tonykoop/djembe/analysis/helmholtz-fem/figures/mode-shapes-L.png

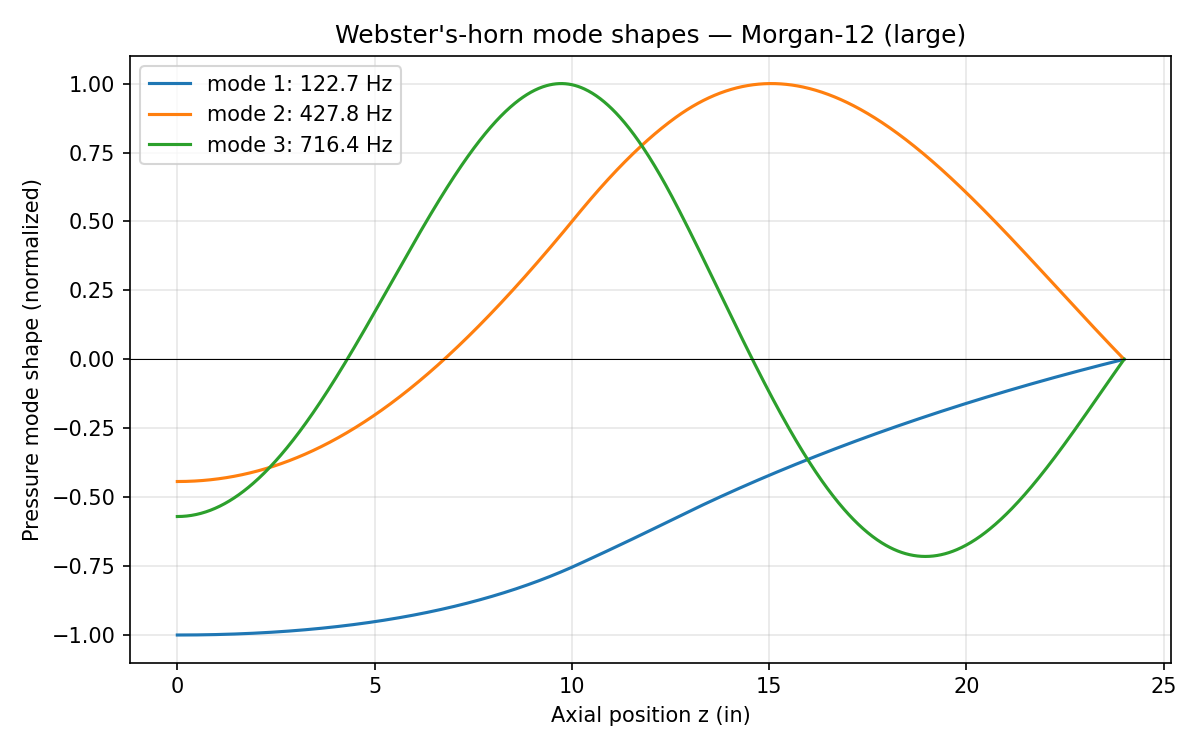
analysis/helmholtz-fem/figures/mode-shapes-L.png
