tonykoop/djembe/arena/round2/stave-djembe-arena-winner.png

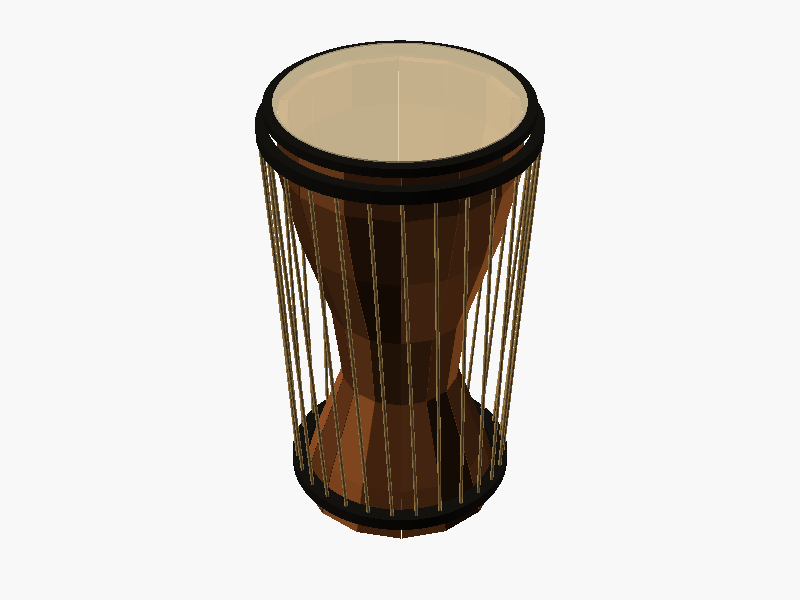
arena/round2/stave-djembe-arena-winner.png
