tonykoop/djembe/CAD/Djembe/Djimbey C.PNG

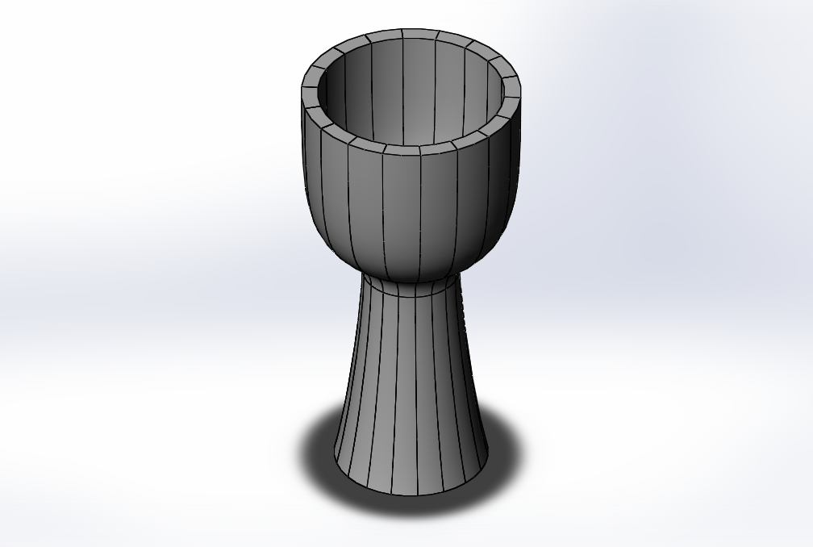
CAD/Djembe/Djimbey C.PNG
