tonykoop/djembe/CAD/Segmented Djembe/large-djembe/Large Djembe Segmented Pattern 1.PNG

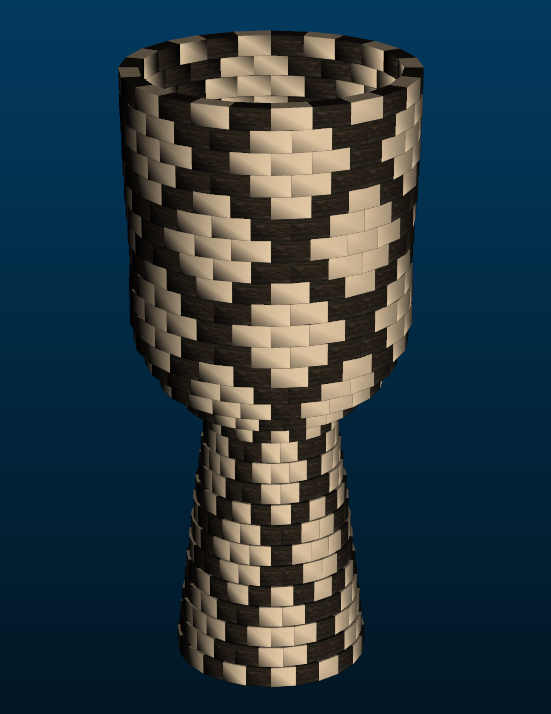
CAD/Segmented Djembe/large-djembe/Large Djembe Segmented Pattern 1.PNG
