tonykoop/djembe/CAD/Segmented Djembe/large-djembe/Large Djembe Segmented Pattern 2.PNG

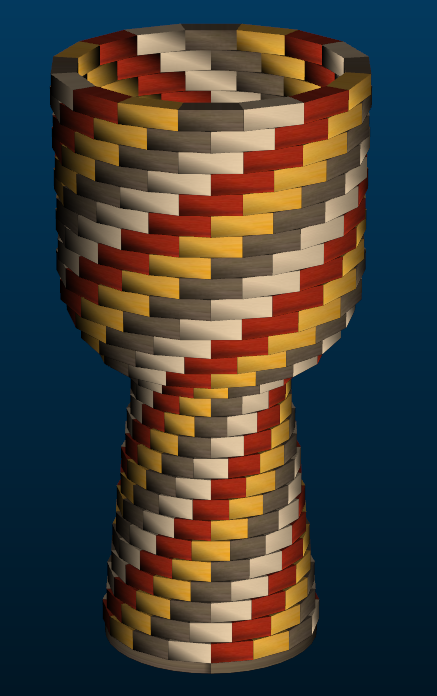
CAD/Segmented Djembe/large-djembe/Large Djembe Segmented Pattern 2.PNG
