tonykoop/djembe/CAD/Segmented Djembe/large-djembe/Large Djembe Segmented Pattern 3.PNG

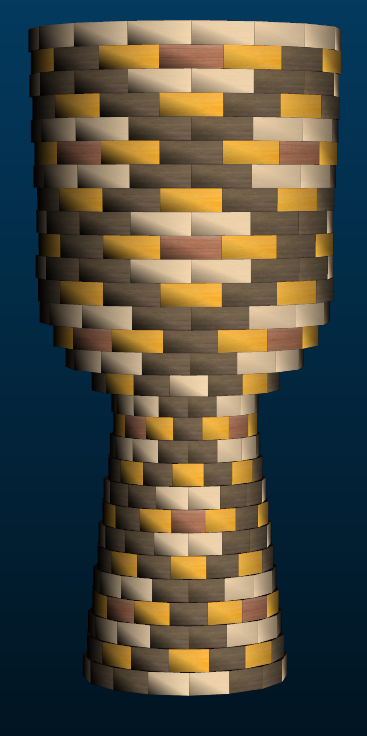
CAD/Segmented Djembe/large-djembe/Large Djembe Segmented Pattern 3.PNG
