tonykoop/djembe/CAD/Segmented Djembe/large-djembe/Large Djembe Segmented Pattern 4.PNG

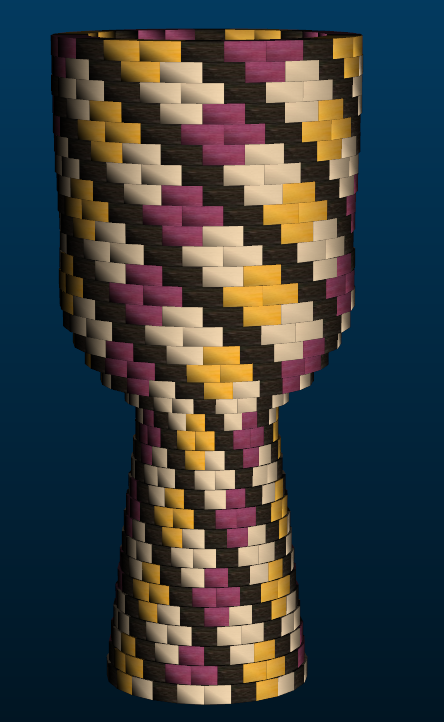
CAD/Segmented Djembe/large-djembe/Large Djembe Segmented Pattern 4.PNG
