tonykoop/djembe/CAD/Segmented Djembe/small-djembe/Small Djembe Segmented Pattern 1.PNG

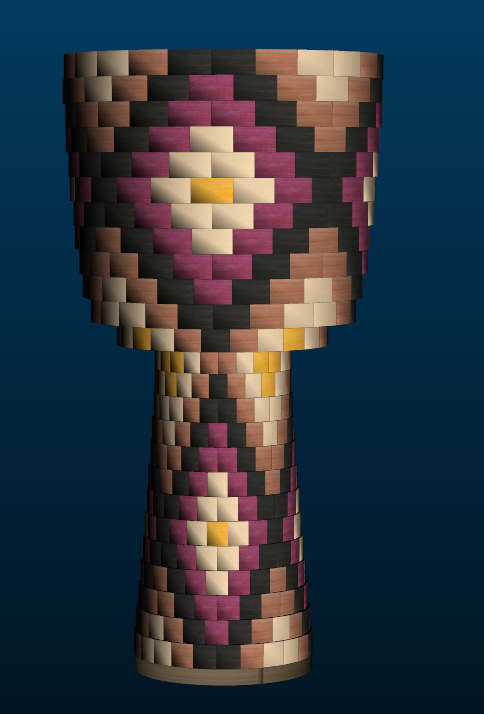
CAD/Segmented Djembe/small-djembe/Small Djembe Segmented Pattern 1.PNG
