tonykoop/djembe/CAD/Segmented Djembe/small-djembe/Small Djembe Segmented Pattern 2.PNG

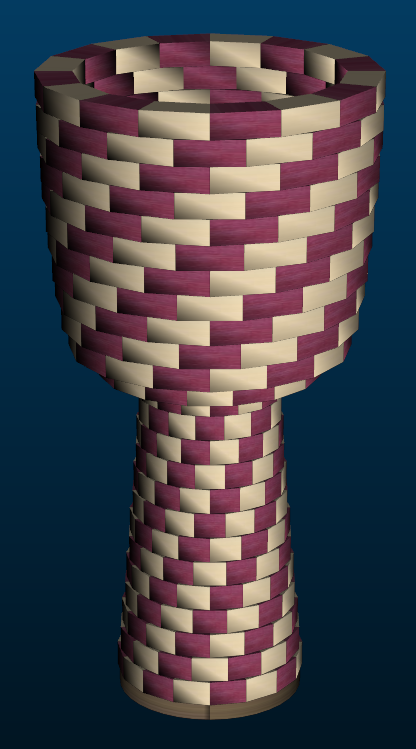
CAD/Segmented Djembe/small-djembe/Small Djembe Segmented Pattern 2.PNG
