tonykoop/djembe/CAD/Segmented Djembe/small-djembe/Small Djembe Segmented Pattern 3.PNG

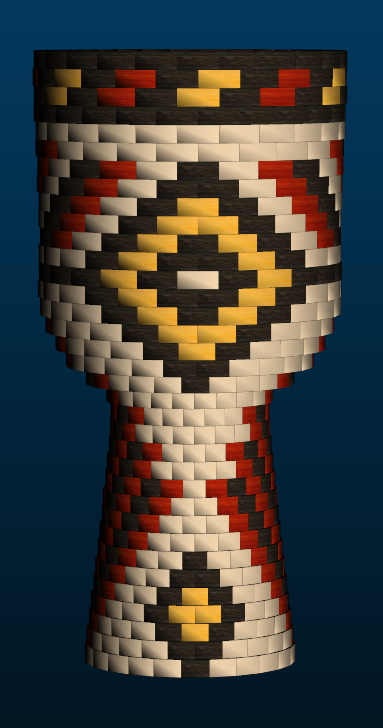
CAD/Segmented Djembe/small-djembe/Small Djembe Segmented Pattern 3.PNG
