tonykoop/djembe/drawings/img20260425_23594038.png

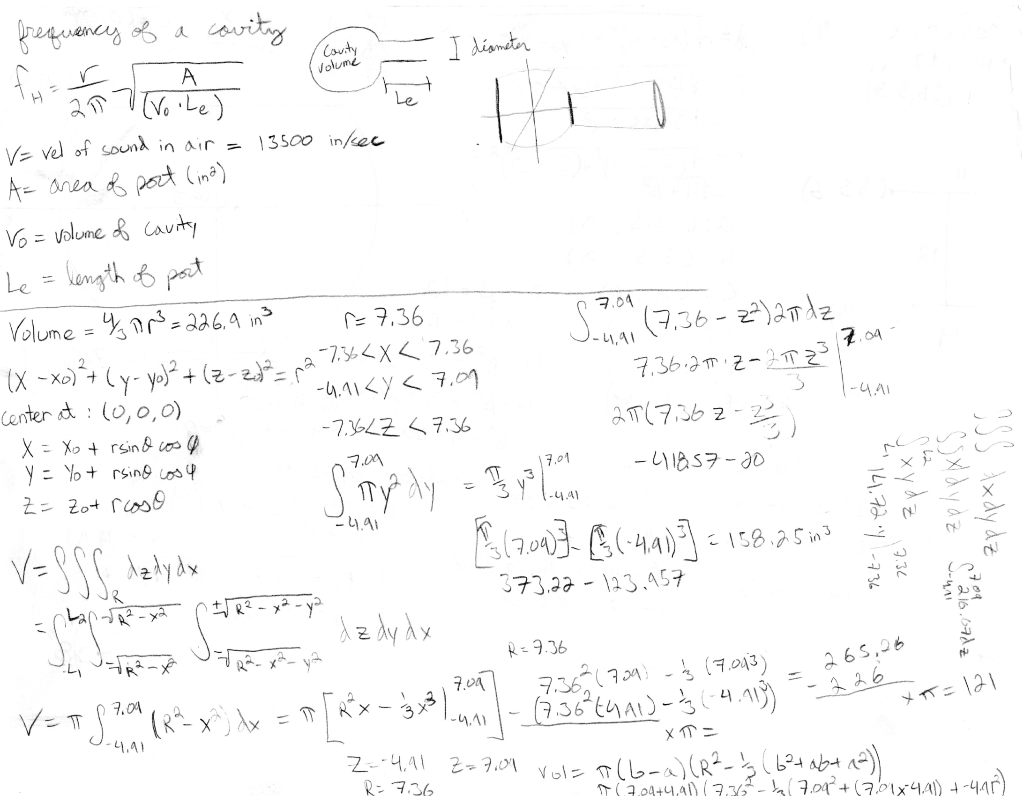
drawings/img20260425_23594038.png
