tonykoop/djembe/drawings/img20260426_00000252.png

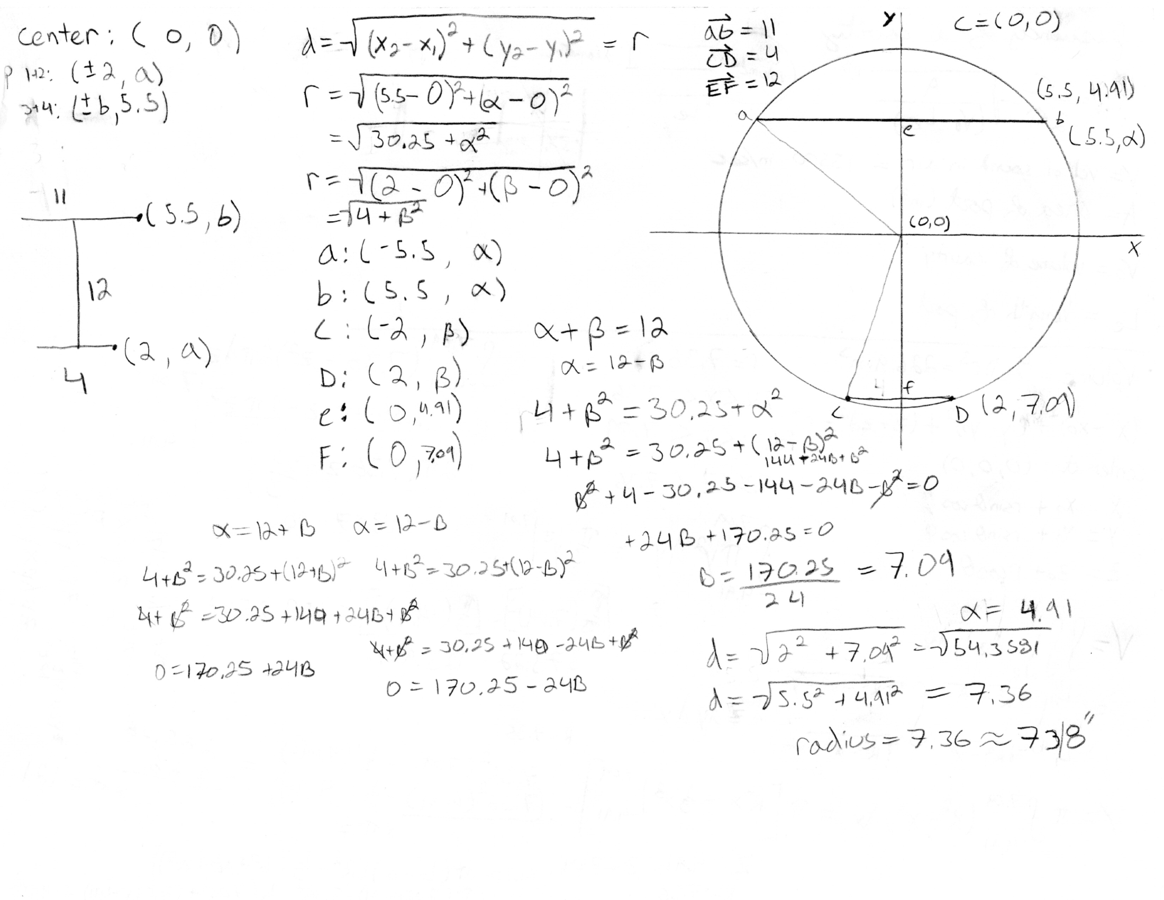
drawings/img20260426_00000252.png
