tonykoop/djembe/drawings/img20260426_00003487.png

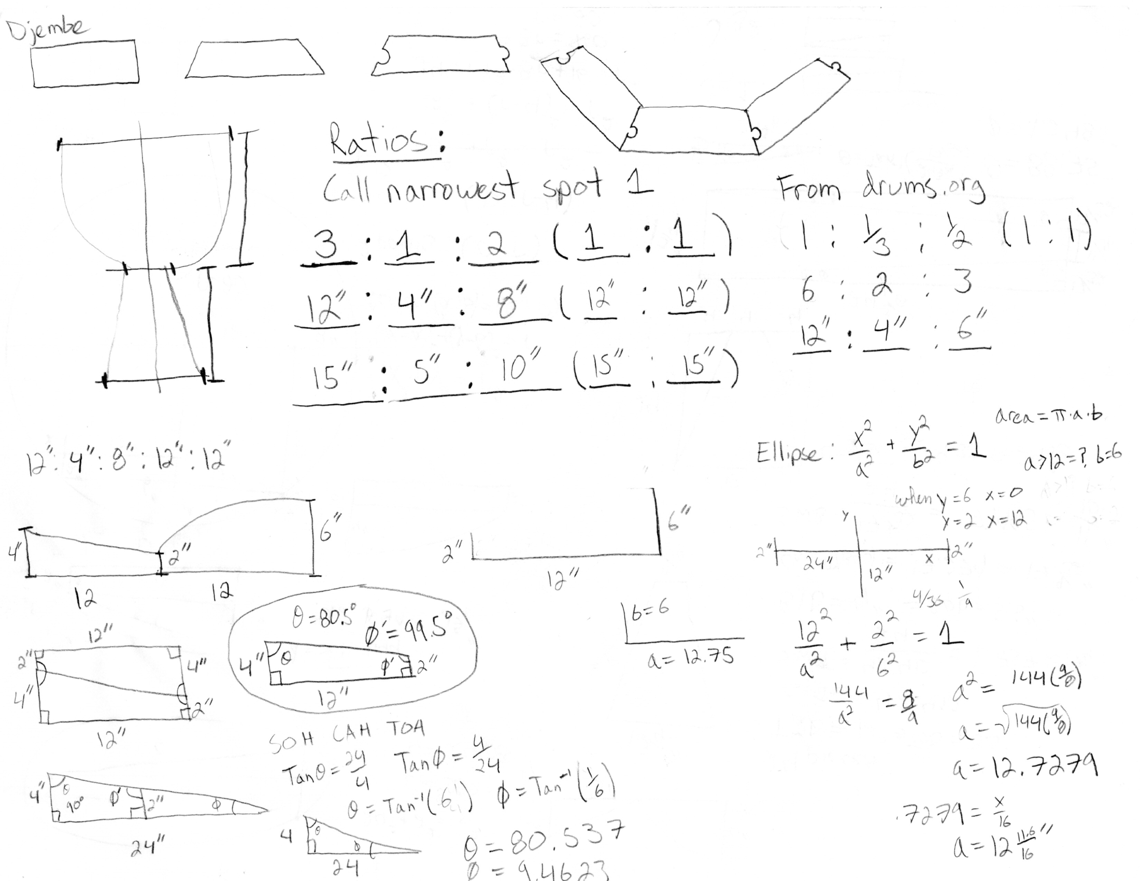
drawings/img20260426_00003487.png
