tonykoop/djembe/drawings/img20260426_00005662.png

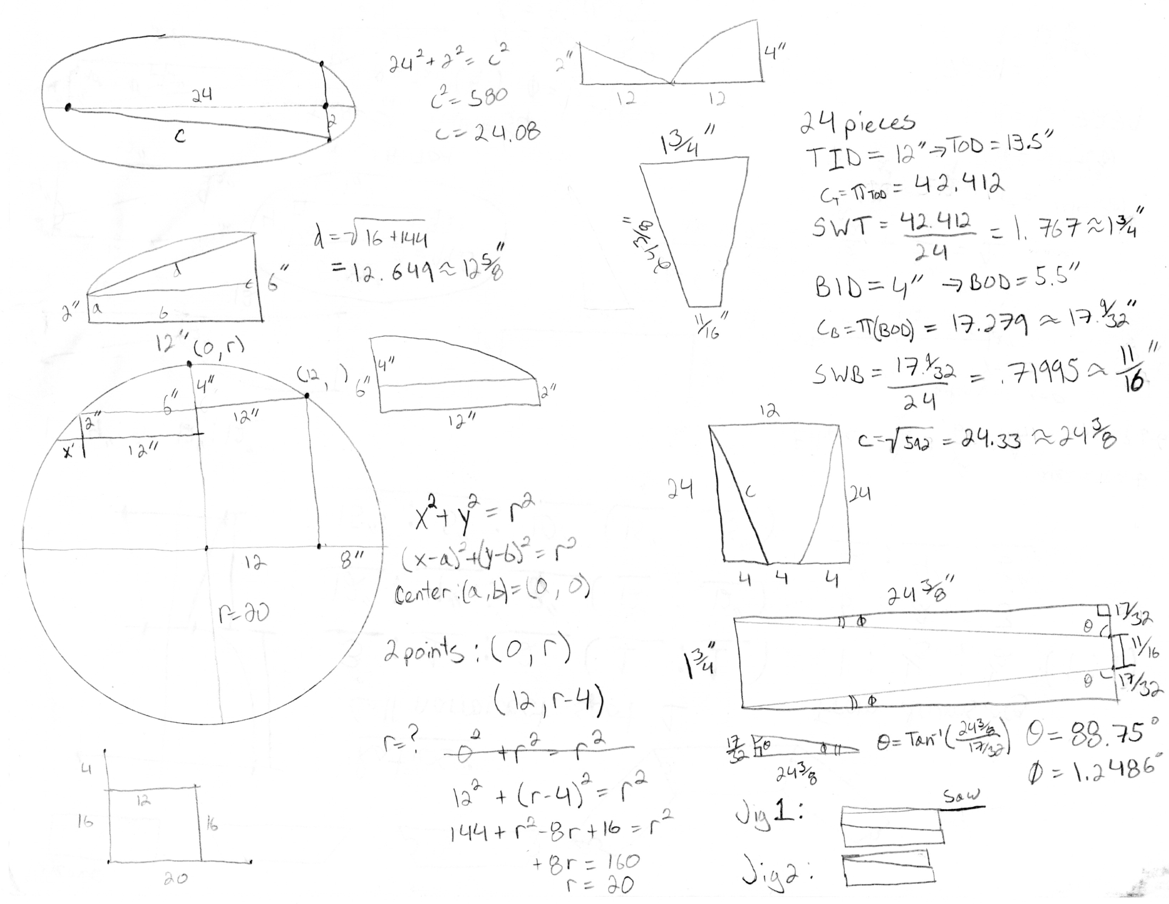
drawings/img20260426_00005662.png
