tonykoop/djembe/drawings/img20260426_00123773.png

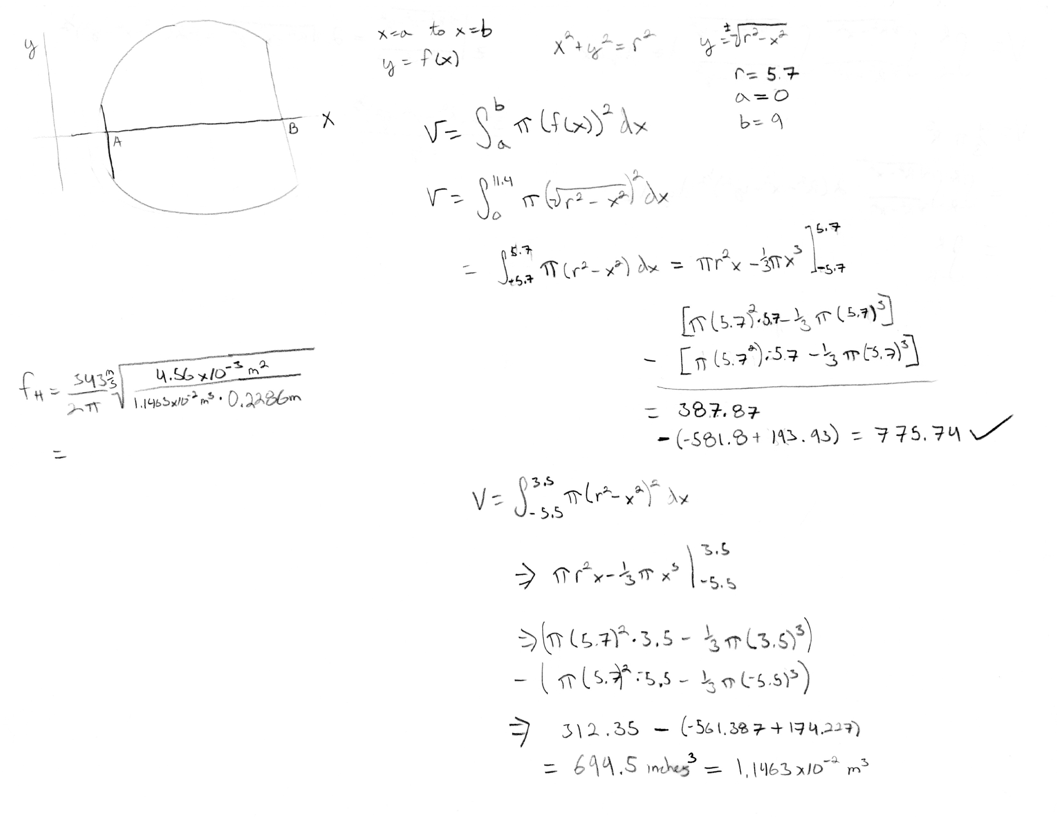
drawings/img20260426_00123773.png
