tonykoop/djembe/drawings/img20260426_00130284.png

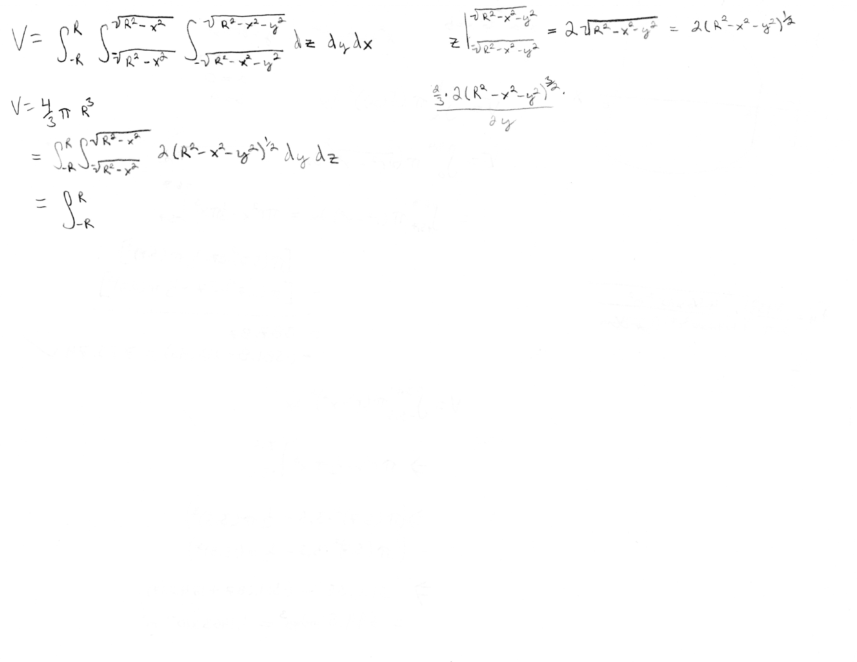
drawings/img20260426_00130284.png
