tonykoop/djembe/drawings/img20260426_00135119.png

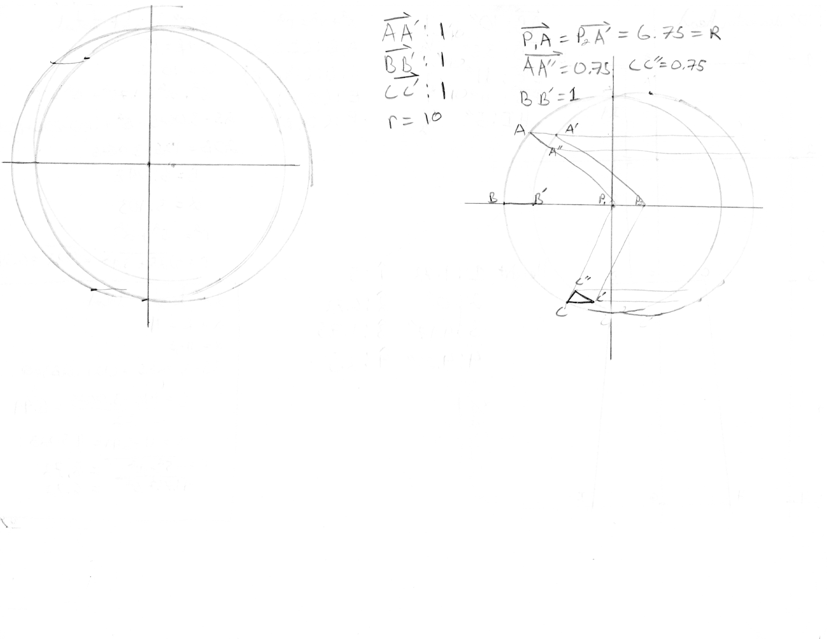
drawings/img20260426_00135119.png
