tonykoop/djembe/drawings/img20260426_00143460.png

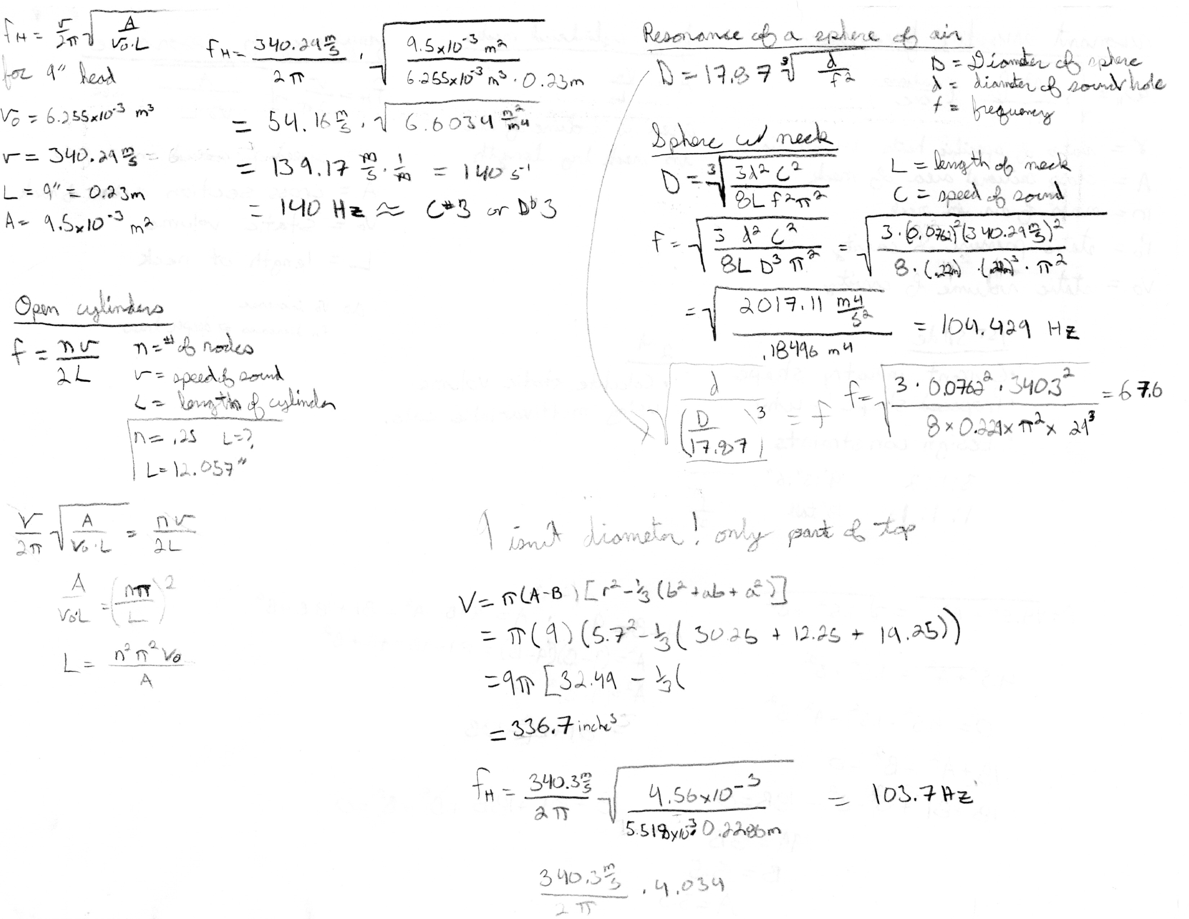
drawings/img20260426_00143460.png
