tonykoop/djembe/validation.csv

gate_id | area | current_status | next_action | evidence_required | pass_condition | blocking_level | notes
DJM-VAL-001 | readiness | bare-bones readiness packet | Review packet files and choose next build path | README plus design.md accepted as scaffold | Scope and authority language remain conservative | L1 blocker | Do not claim build-ready from this packet alone.
DJM-VAL-002 | acoustics-analysis | analysis-only FEM exists | Reproduce analysis run and record command outputs | analysis/helmholtz-fem/results.csv and reproduced logs | Solver check passes and generated outputs match committed tables | L2 gate | This validates analysis reproducibility not a physical drum.
DJM-VAL-003 | strike-measurement | not recorded | Measure bass tone open tone and slap on a known drum | Mic setup FFT method room notes head size and repeated strikes | Repeatable frequencies and spectra are logged | L3 gate | Required before empirical acoustic claims.
DJM-VAL-004 | shell-geometry | derived and archival references exist | Choose target S M or L profile and capture measured dimensions | calipers tape photo scale CAD or design table review | Head diameter neck diameter foot diameter height and profile basis are recorded | L2 gate | Parametric CSV is a reference until reviewed for fabrication.
DJM-VAL-005 | head-tension | not recorded | Document head material collar fit and tuning state | head photos tension method rope pattern and before-after tuning notes | Head setup is reproducible and tied to strike measurements | L3 gate | Membrane modes depend on tension and material.
DJM-VAL-006 | construction-path | not selected | Choose segmented stack curved staves or lathe-finished shell | decision record plus sketch or CAD authority | One path has clear next drawings and cut list | L2 gate | Do not mix path-specific dimensions without review.
DJM-VAL-007 | jig-safety | not started | Define jig operation and safety checks | tool list workholding plan guards PPE and test scrap record | Fixture trial on scrap passes before instrument stock | L3 gate | Router and lathe operations need shop validation.
DJM-VAL-008 | sourcing | unverified | Check current suppliers at purchase time | dated supplier screenshots quotes or in-hand inventory | BOM rows are updated with verified source status | L2 gate | No current price or availability claims in this packet.
DJM-VAL-009 | documentation | started | Photograph evidence and authority artifacts | photo-shotlist.md completion with captions and scale where needed | Images show provenance process and measurement context | L2 gate | Photos are documentation unless scale and measurement authority are explicit.
DJM-VAL-010 | validation-loop | measurement-required | Fill validation-loop.csv with measured bass open-tone slap shell head and tension rows | dated measurement logs photos audio files and command outputs | Each critical claim has method measured_result status next_action and evidence | L3 gate | This is the issue #4 next-build data surface.
DJM-VAL-011 | visual-authority | reference-only register added | Run visual authority validator and keep visuals out of fabrication claims | visual-output-register.csv validator output | Photos scans figures and previews validate as non-authority rows | L2 gate | Add fabrication-authority rows only after reviewed CAD DXF drawings design tables or measured templates exist.
