tonykoop/djembe/images/20210320_133754.jpg

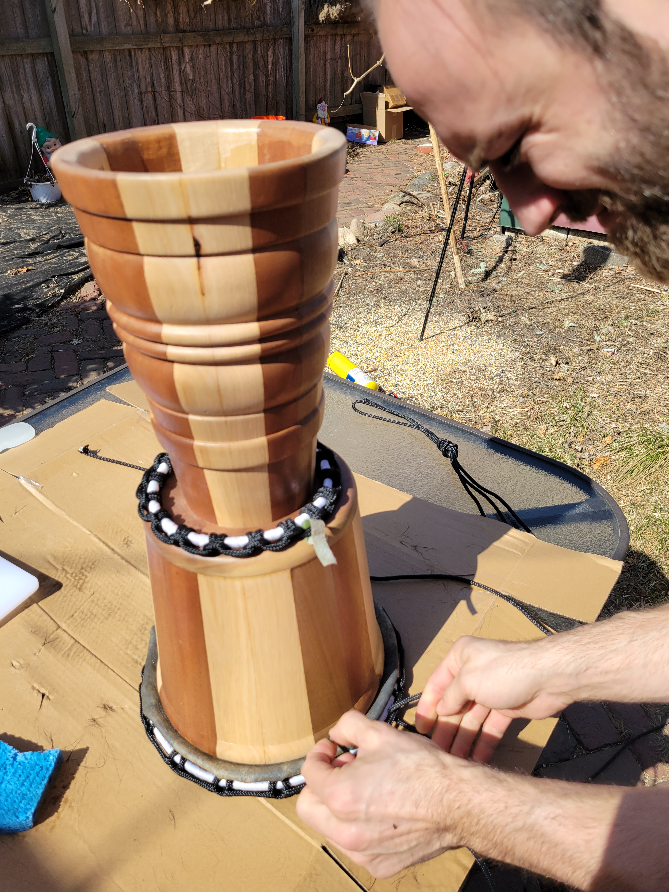
images/20210320_133754.jpg
