tonykoop/djembe/images/20210320_133755.jpg

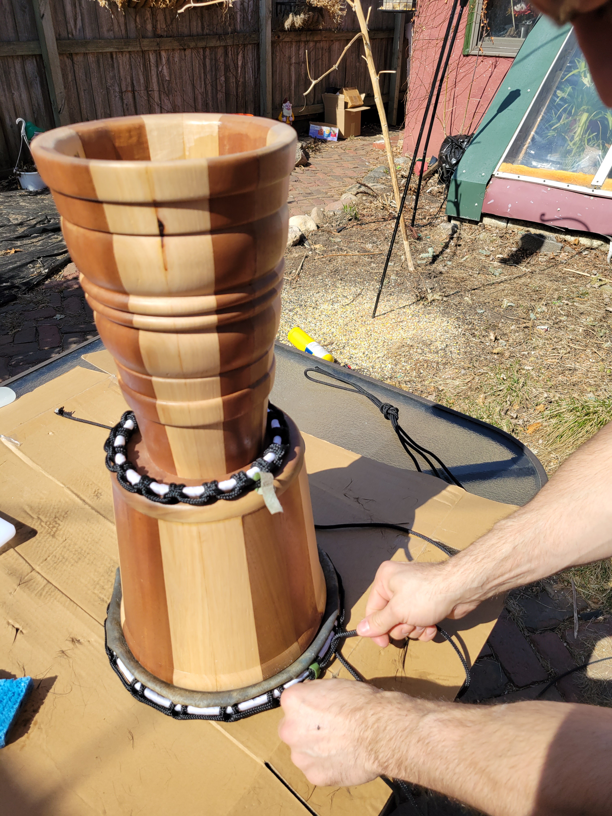
images/20210320_133755.jpg
