tonykoop/djembe/images/20210320_133803.jpg

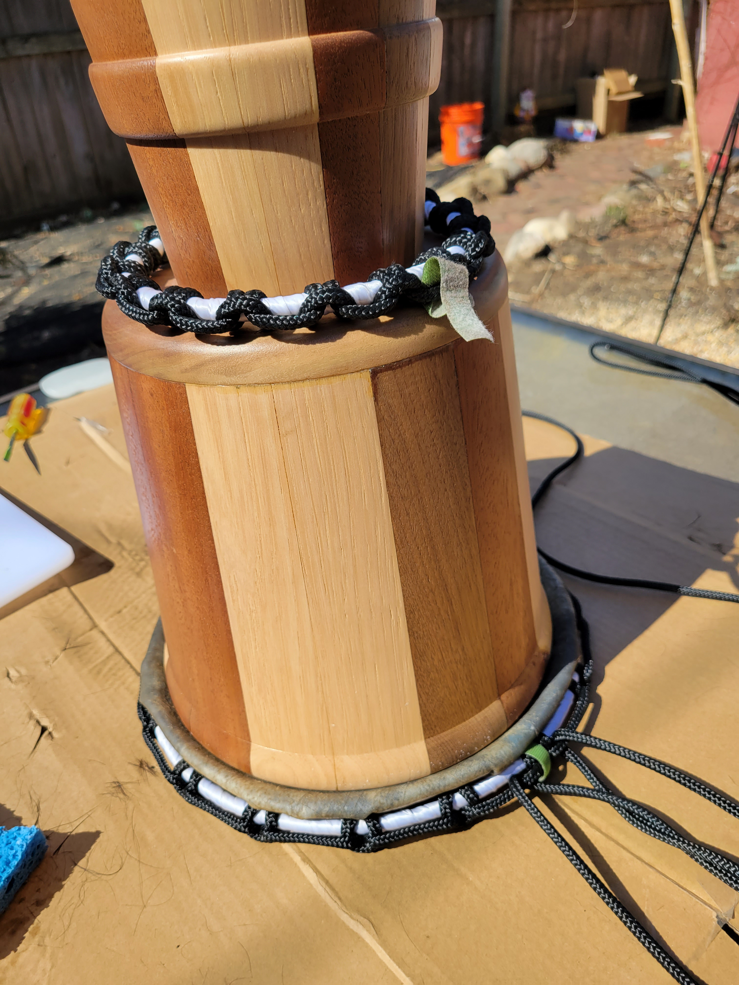
images/20210320_133803.jpg
