tonykoop/djembe/images/20210320_151206.jpg

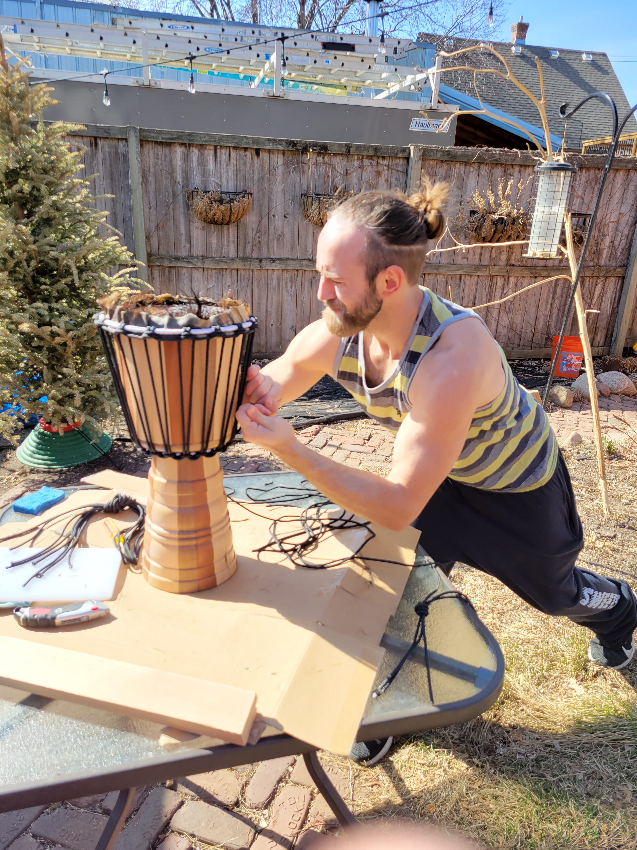
images/20210320_151206.jpg
